ivajon/E7020E_gaming_mouse/code/e7020e_rtic/src/srom.rs

// const unsigned char firmware_data[] PROGMEM
pub const FIRMWARE_C: [u8; 4094] = [
    0x01, 0x06, 0x88, 0x9e, 0x7e, 0x4c, 0x7e, 0x7e, 0x7e, 0x5f, 0x1d, 0xb8, 0xf2, 0x66, 0x2f, 0xdc,
    0x3a, 0xd7, 0x2c, 0xba, 0xf4, 0x4b, 0x16, 0x8b, 0x75, 0x68, 0x33, 0xe4, 0x2b, 0xd4, 0x2a, 0xb7,
    0xec, 0x5a, 0x36, 0xcf, 0xfd, 0x59, 0x11, 0xa0, 0xc2, 0xe7, 0x4c, 0x1a, 0x97, 0xac, 0xda, 0x17,
    0xac, 0xda, 0x17, 0xac, 0xda, 0x36, 0xee, 0x3f, 0xdd, 0x38, 0xd3, 0x05, 0x88, 0x73, 0x64, 0x4a,
    0x16, 0x8f, 0x7d, 0x7b, 0x72, 0x66, 0x4e, 0x1e, 0xbe, 0xfe, 0x5f, 0x1d, 0x99, 0x91, 0x81, 0x61,
    0x25, 0xa1, 0xc0, 0xe3, 0x25, 0xc8, 0x12, 0xa6, 0xaf, 0xdc, 0x3a, 0xf6, 0x4f, 0xfd, 0x78, 0x53,
    0x05, 0x88, 0x92, 0x87, 0x6d, 0x39, 0xd1, 0x01, 0x80, 0x66, 0x25, 0xc8, 0x12, 0x87, 0x6d, 0x58,
    0x32, 0xe6, 0x4e, 0xff, 0x5d, 0x38, 0xd3, 0x05, 0x69, 0x31, 0xc1, 0x00, 0x82, 0x80, 0x6f, 0x5c,
    0x57, 0x6d, 0x60, 0xd6, 0xcd, 0x0f, 0x90, 0x09, 0x00, 0xb6, 0x52, 0xa4, 0xe8, 0x59, 0x3c, 0x61,
    0x9e, 0x9b, 0x77, 0x9e, 0xff, 0x11, 0x6d, 0x0f, 0x16, 0x14, 0x11, 0x73, 0xb9, 0x2a, 0x53, 0x29,
    0xc2, 0xa8, 0x22, 0xc0, 0x17, 0xa0, 0x95, 0x0f, 0x80, 0xe2, 0x93, 0xa8, 0x84, 0x43, 0x8f, 0xb7,
    0xc7, 0x67, 0xe2, 0xa9, 0xbe, 0xe9, 0x7e, 0x16, 0x23, 0x33, 0xba, 0x18, 0x3b, 0xd0, 0xce, 0xbc,
    0x0e, 0xe7, 0xbb, 0xec, 0x5f, 0xf1, 0xc2, 0xd7, 0x5d, 0x5a, 0xc6, 0x0b, 0x78, 0xd0, 0xb3, 0xb4,
    0x7c, 0x62, 0x62, 0xcb, 0x3d, 0x5a, 0xd6, 0xf1, 0x89, 0x83, 0xc7, 0x5f, 0x94, 0xfb, 0xec, 0x3a,
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
    0x7d, 0x85, 0xea, 0x95, 0x2f, 0xc0, 0xe8, 0x6f, 0x35, 0xa0, 0x3a, 0x02, 0x25, 0xbc, 0xb2, 0x5f,
    0x5c, 0x43, 0x96, 0xcc, 0x26, 0xd2, 0x16, 0xb4, 0x96, 0x73, 0xd7, 0x13, 0xc7, 0xae, 0x53, 0x15,
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
];
