ivajon/E7020E_gaming_mouse/code/e7020e_rtic/src/lib.rs

#![no_std]
/// The sensor driver
pub mod pmw3389;
/// The rbg driver
pub mod pca9624_pw;
/// The hid driver
pub mod mouseReport;
/// The hid driver
pub mod mouseKeyboardReport;
pub mod hidDescriptors;
pub mod macroSystem;
pub mod srom;
pub mod rgb_pattern_things;
pub mod matr_math;
pub mod color;
