ivajon/E7020E_gaming_mouse/code/mouse_firmware/src/hidDescriptors.rs

use usbd_hid::{descriptor::generator_prelude::*, hid_class::HIDClass};

#[gen_hid_descriptor(
    (collection = APPLICATION, usage_page = GENERIC_DESKTOP, usage = 0x00) = {
        (collection = PHYSICAL, usage = POINTER) = {
            (usage_page = BUTTON, usage_min = BUTTON_1, usage_max = BUTTON_8) = {
                #[packed_bits 8] #[item_settings data,variable,absolute] buttons=input;
            };
            (usage_page = GENERIC_DESKTOP,) = {
                (usage = X,) = {
                    #[item_settings data,variable,relative] x=input;
                };
                (usage = Y,) = {
                    #[item_settings data,variable,relative] y=input;
                };
                (usage = WHEEL,) = {
                    #[item_settings data,variable,relative] wheel=input;
                };
            };
            (usage_page = CONSUMER,) = {
                (usage = AC_PAN,) = {
                    #[item_settings data,variable,relative] pan=input;
                };
            };
        };
        (usage_page = KEYBOARD, usage_min = 0xE0, usage_max = 0xE7) = {
            #[packed_bits 8] #[item_settings data,variable,absolute] modifier=input;
        };
        (usage_min = 0x00, usage_max = 0xFF) = {
            #[item_settings constant,variable,absolute] reserved=input;
        };
        (usage_page = LEDS, usage_min = 0x01, usage_max = 0x05) = {
            #[packed_bits 5] #[item_settings data,variable,absolute] leds=output;
        };
        (usage_page = KEYBOARD, usage_min = 0x00, usage_max = 0xDD) = {
            #[item_settings data,array,absolute] keycodes=input;
        };
    }
)]

pub struct MouseKeyboard {
    pub buttons: u8,
    pub x: i8,
    pub y: i8,
    pub wheel: i8, // Scroll down (negative) or up (positive) this many units
    pub pan: i8,   // Scroll left (negative) or right (positive) this many units
    //
    pub modifier: u8,
    pub reserved: u8,
    pub leds: u8,
    pub keycodes: [u8; 6],
}
