ivajon/E7020E_gaming_mouse/code/e7020e_rtic/examples/rtic_usb_serial.rs

//! CDC-ACM serial port example using polling in a busy loop.
//! Target board: any STM32F4 with a OTG FS peripheral and a 25MHz HSE crystal
#![no_std]
#![no_main]

use panic_semihosting as _;

#[rtic::app(device = stm32f4::stm32f401, dispatchers = [EXTI0])]
mod app {
    use stm32f4xx_hal::otg_fs::{UsbBus, USB};
    use stm32f4xx_hal::prelude::*;
    use usb_device::prelude::*;

    #[shared]
    struct Shared {}

    #[local]
    struct Local {}
    #[init(local = [EP_MEMORY: [u32; 1024] = [0; 1024]])]
    fn init(cx: init::Context) -> (Shared, Local, init::Monotonics) {
        let dp = cx.device;

        let rcc = dp.RCC.constrain();

        let clocks = rcc.cfgr.sysclk(48.MHz()).require_pll48clk().freeze();

        let gpioa = dp.GPIOA.split();

        let usb = USB {
            usb_global: dp.OTG_FS_GLOBAL,
            usb_device: dp.OTG_FS_DEVICE,
            usb_pwrclk: dp.OTG_FS_PWRCLK,
            pin_dm: gpioa.pa11.into_alternate(),
            pin_dp: gpioa.pa12.into_alternate(),
            hclk: clocks.hclk(),
        };

        let usb_bus = UsbBus::new(usb, cx.local.EP_MEMORY);

        let mut serial = usbd_serial::SerialPort::new(&usb_bus);

        let mut usb_dev = UsbDeviceBuilder::new(&usb_bus, UsbVidPid(0x16c0, 0x27dd))
            .manufacturer("e7020e")
            .product("Serial port")
            .serial_number("1337")
            .device_class(usbd_serial::USB_CLASS_CDC)
            .build();

        loop {
            if !usb_dev.poll(&mut [&mut serial]) {
                continue;
            }

            let mut buf = [0u8; 64];

            match serial.read(&mut buf) {
                Ok(count) if count > 0 => {
                    // Echo back in upper case
                    for c in buf[0..count].iter_mut() {
                        if 0x61 <= *c && *c <= 0x7a {
                            *c &= !0x20;
                        }
                    }

                    let mut write_offset = 0;
                    while write_offset < count {
                        match serial.write(&buf[write_offset..count]) {
                            Ok(len) if len > 0 => {
                                write_offset += len;
                            }
                            _ => {}
                        }
                    }
                }
                _ => {}
            }
        }

        (Shared {}, Local {}, init::Monotonics())
    }
}
